erikbakke/AmigaKeyboard/Firmware/AmigaKeyboard/AmigaKeyboard/src/config/conf_clock.h

/**
 * \file
 *
 * \brief Chip-specific system clock manager configuration
 *
 * Copyright (c) 2014-2018 Microchip Technology Inc. and its subsidiaries.
 *
 * \asf_license_start
 *
 * \page License
 *
 * Subject to your compliance with these terms, you may use Microchip
 * software and any derivatives exclusively with Microchip products.
 * It is your responsibility to comply with third party license terms applicable
 * to your use of third party software (including open source software) that
 * may accompany Microchip software.
 *
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
 * \asf_license_stop
 *
 */
/*
 * Support and FAQ: visit <a href="https://www.microchip.com/support/">Microchip Support</a>
 */
#ifndef CONF_CLOCK_H_INCLUDED
#define CONF_CLOCK_H_INCLUDED

/* ===== System Clock Source Options */
#define SYSCLK_SRC_RC16MHZ    0
#define SYSCLK_SRC_RC128KHZ   1
#define SYSCLK_SRC_TRS16MHZ   2
#define SYSCLK_SRC_RC32KHZ    3
#define SYSCLK_SRC_XOC16MHZ   4
#define SYSCLK_SRC_EXTERNAL   5

/* =====  Select connected clock source */
/* #define  SYSCLK_SOURCE         SYSCLK_SRC_RC16MHZ */
/* #define SYSCLK_SOURCE        SYSCLK_SRC_RC128KHZ */
/* #define SYSCLK_SOURCE        SYSCLK_SRC_TRS16MHZ */
#define SYSCLK_SOURCE        SYSCLK_SRC_XOC16MHZ

/* ===== System Clock Bus Division Options */
#define CONFIG_SYSCLK_PSDIV         SYSCLK_PSDIV_1

#define F_CPU ( 8000000 )
#endif /* CONF_CLOCK_H_INCLUDED */
